ebubekirtascieee/Custom-1240MHz-SDR-PCB-and-Software/Simulations and Measurements/Input_HighPass_Filter.png

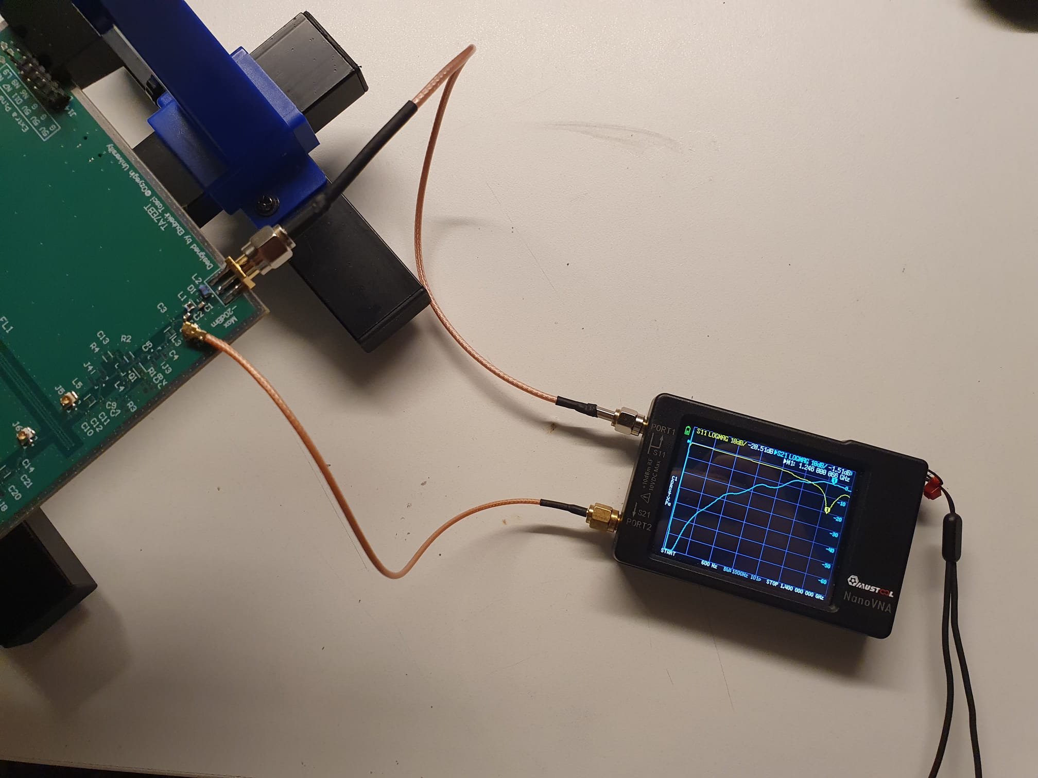
Simulations and Measurements/Input_HighPass_Filter.png
