ebubekirtascieee/Custom-1240MHz-SDR-PCB-and-Software/Simulations and Measurements/IF_AMP.asc

C1: cap; 100nF
C2: cap; 100n
C3: cap; 100n
C5: cap; 100n
C6: cap; 100n
R1: res; 50
R2: res; 51
R3: res; 10k
R4: res; 10k
R5: res; 1k
R6: res; 33
R7: res; 50
R8: res; 10k
R9: res; 10k
R10: res; 1k
R11: res; 33
R12: res; 10k
R13: res; 4.4k
U1: UniversalOpAmp; Avol=1Meg GBW=800Meg Vos=0
U2: UniversalOpAmp; Avol=1Meg GBW=800Meg Vos=0
V1: voltage; SINE(0 1mV 10e6)
V2: voltage; 3.3V
V3: voltage; 3.3V
V4: voltage; 3.3V
Named nets: 0
.tran 1
