ebubekirtascieee/Custom-1240MHz-SDR-PCB-and-Software/FPGA_Files/src/fft/temp/FFT/twIm.v

16'd0,
16'd65335,
16'd65134,
16'd64933,
16'd64732,
16'd64531,
16'd64330,
16'd64129,
16'd63928,
16'd63727,
16'd63527,
16'd63326,
16'd63126,
16'd62925,
16'd62725,
16'd62524,
16'd62324,
16'd62124,
16'd61924,
16'd61725,
16'd61525,
16'd61326,
16'd61126,
16'd60927,
16'd60728,
16'd60529,
16'd60331,
16'd60132,
16'd59934,
16'd59736,
16'd59538,
16'd59341,
16'd59143,
16'd58946,
16'd58750,
16'd58553,
16'd58357,
16'd58161,
16'd57965,
16'd57769,
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
