ebubekirtascieee/Custom-1240MHz-SDR-PCB-and-Software/FPGA_Files/src/gowin_sdpb_fft/gowin_sdpb_fft.v

//Copyright (C)2014-2025 Gowin Semiconductor Corporation.
//All rights reserved.
//File Title: IP file
//Tool Version: V1.9.11.01 Education (64-bit)
//Part Number: GW2A-LV18PG256C8/I7
//Device: GW2A-18
//Device Version: C
//Created Time: Wed Apr  1 03:07:17 2026

module Gowin_SDPB_fft (dout, clka, cea, reseta, clkb, ceb, resetb, oce, ada, din, adb);

output [15:0] dout;
input clka;
input cea;
input reseta;
input clkb;
input ceb;
input resetb;
input oce;
input [10:0] ada;
input [15:0] din;
input [10:0] adb;

wire [23:0] sdpb_inst_0_dout_w;
wire [23:0] sdpb_inst_1_dout_w;
wire gw_gnd;

assign gw_gnd = 1'b0;

SDPB sdpb_inst_0 (
    .DO({sdpb_inst_0_dout_w[23:0],dout[7:0]}),
    .CLKA(clka),
    .CEA(cea),
    .RESETA(reseta),
    .CLKB(clkb),
    .CEB(ceb),
    .RESETB(resetb),
    .OCE(oce),
    .BLKSELA({gw_gnd,gw_gnd,gw_gnd}),
    .BLKSELB({gw_gnd,gw_gnd,gw_gnd}),
    .ADA({ada[10:0],gw_gnd,gw_gnd,gw_gnd}),
    .DI({gw_gnd,gw_gnd,gw_gnd,gw_gnd,gw_gnd,gw_gnd,gw_gnd,gw_gnd,gw_gnd,gw_gnd,gw_gnd,gw_gnd,gw_gnd,gw_gnd,gw_gnd,gw_gnd,gw_gnd,gw_gnd,gw_gnd,gw_gnd,gw_gnd,gw_gnd,gw_gnd,gw_gnd,din[7:0]}),
    .ADB({adb[10:0],gw_gnd,gw_gnd,gw_gnd})
);

defparam sdpb_inst_0.READ_MODE = 1'b0;
defparam sdpb_inst_0.BIT_WIDTH_0 = 8;
defparam sdpb_inst_0.BIT_WIDTH_1 = 8;
defparam sdpb_inst_0.BLK_SEL_0 = 3'b000;
defparam sdpb_inst_0.BLK_SEL_1 = 3'b000;
defparam sdpb_inst_0.RESET_MODE = "SYNC";

SDPB sdpb_inst_1 (
    .DO({sdpb_inst_1_dout_w[23:0],dout[15:8]}),
    .CLKA(clka),
    .CEA(cea),
    .RESETA(reseta),
    .CLKB(clkb),
    .CEB(ceb),
    .RESETB(resetb),
    .OCE(oce),
    .BLKSELA({gw_gnd,gw_gnd,gw_gnd}),
    .BLKSELB({gw_gnd,gw_gnd,gw_gnd}),
    .ADA({ada[10:0],gw_gnd,gw_gnd,gw_gnd}),
    .DI({gw_gnd,gw_gnd,gw_gnd,gw_gnd,gw_gnd,gw_gnd,gw_gnd,gw_gnd,gw_gnd,gw_gnd,gw_gnd,gw_gnd,gw_gnd,gw_gnd,gw_gnd,gw_gnd,gw_gnd,gw_gnd,gw_gnd,gw_gnd,gw_gnd,gw_gnd,gw_gnd,gw_gnd,din[15:8]}),
    .ADB({adb[10:0],gw_gnd,gw_gnd,gw_gnd})
);

defparam sdpb_inst_1.READ_MODE = 1'b0;
defparam sdpb_inst_1.BIT_WIDTH_0 = 8;
defparam sdpb_inst_1.BIT_WIDTH_1 = 8;
defparam sdpb_inst_1.BLK_SEL_0 = 3'b000;
defparam sdpb_inst_1.BLK_SEL_1 = 3'b000;
defparam sdpb_inst_1.RESET_MODE = "SYNC";

endmodule //Gowin_SDPB_fft
