ebubekirtascieee/Custom-1240MHz-SDR-PCB-and-Software/FPGA_Files/src/cordic/cordic_tmp.v

//Copyright (C)2014-2025 Gowin Semiconductor Corporation.
//All rights reserved.
//File Title: Template file for instantiation
//Tool Version: V1.9.11.01 Education (64-bit)
//Part Number: GW2A-LV18PG256C8/I7
//Device: GW2A-18
//Device Version: C
//Created Time: Wed Apr  1 17:32:08 2026

//Change the instance name and port connections to the signal names
//--------Copy here to design--------

	CORDIC_Top your_instance_name(
		.clk(clk), //input clk
		.rst(rst), //input rst
		.x_i(x_i), //input [16:0] x_i
		.y_i(y_i), //input [16:0] y_i
		.theta_i(theta_i), //input [16:0] theta_i
		.x_o(x_o), //output [16:0] x_o
		.y_o(y_o), //output [16:0] y_o
		.theta_o(theta_o) //output [16:0] theta_o
	);

//--------Copy end-------------------
