ebubekirtascieee/Custom-1240MHz-SDR-PCB-and-Software/FPGA_Files/src/fft/fft_tmp.v

//Copyright (C)2014-2025 Gowin Semiconductor Corporation.
//All rights reserved.
//File Title: Template file for instantiation
//Tool Version: V1.9.11.01 Education (64-bit)
//Part Number: GW2A-LV18PG256C8/I7
//Device: GW2A-18
//Device Version: C
//Created Time: Wed Apr  1 03:27:37 2026

//Change the instance name and port connections to the signal names
//--------Copy here to design--------

	FFT_Top your_instance_name(
		.idx(idx), //output [9:0] idx
		.xk_re(xk_re), //output [15:0] xk_re
		.xk_im(xk_im), //output [15:0] xk_im
		.sod(sod), //output sod
		.ipd(ipd), //output ipd
		.eod(eod), //output eod
		.busy(busy), //output busy
		.soud(soud), //output soud
		.opd(opd), //output opd
		.eoud(eoud), //output eoud
		.xn_re(xn_re), //input [15:0] xn_re
		.xn_im(xn_im), //input [15:0] xn_im
		.start(start), //input start
		.clk(clk), //input clk
		.rst(rst) //input rst
	);

//--------Copy end-------------------
