ebubekirtascieee/Custom-1240MHz-SDR-PCB-and-Software/FPGA_Files/src/fft/temp/FFT/defile.v

`define MODULE_NAME FFT_Top
`define FIXED
`define FFT1024
`define POINTS 1024
`define POINTS_LOG 10
`define TARGET_DEVICE_GW1A2A
`define MODE_FORWARD
`define OUTPUT_NATURAL
`define SCALING_RS111
`define INPUT_DATA_WIDTH 16
`define INPUT_DATA_WIDTH_LOG 4
`define TWIDDLE_FACTOR_WIDTH 16
`define TWIDDLE_FACTOR_WIDTH_LOG 4
`define OUTPUT_DATA_WIDTH 16
`define OUTPUT_DATA_WIDTH_LOG 4
`define REDUCTION_TRUNCATION
`define DSP_BLOCK_BASED
`define EBR_MEMORY
`define TDF_EBR_MEMORY
